zeitinfarkt/wallbox-power-management/doc/cad/DIN Rail Mount PI-LCD/snapshots/clip.jpg

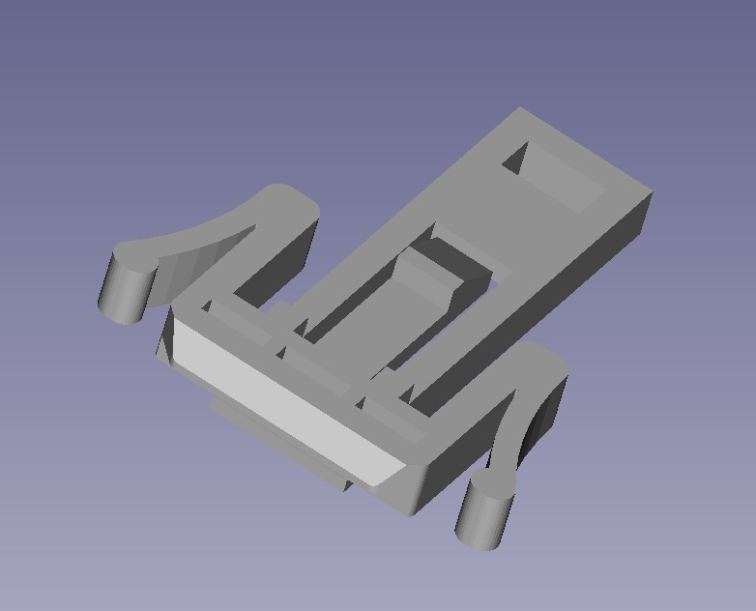
doc/cad/DIN Rail Mount PI-LCD/snapshots/clip.jpg
