zeitinfarkt/wallbox-power-management/doc/cad/DIN Rail Mount PI-LCD/snapshots/cover.jpg

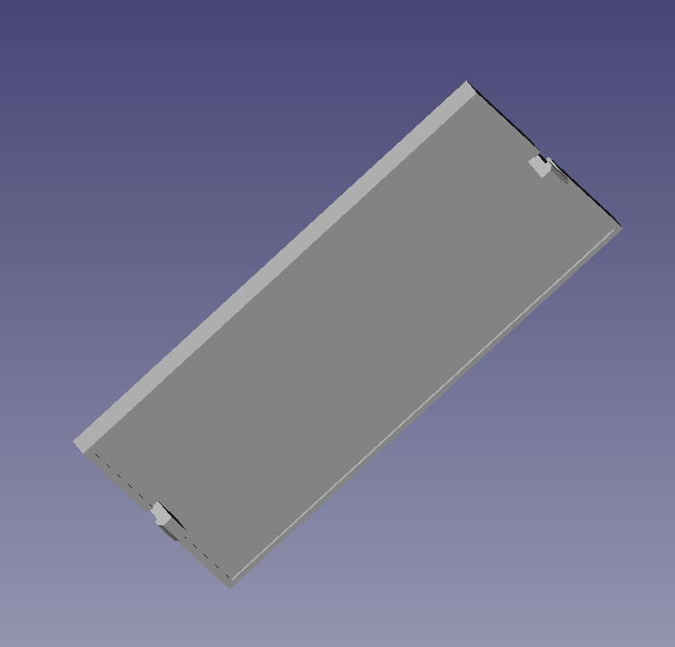
doc/cad/DIN Rail Mount PI-LCD/snapshots/cover.jpg
